tebl/RC-Light-System/documentation/datasheet/rgb_led.png

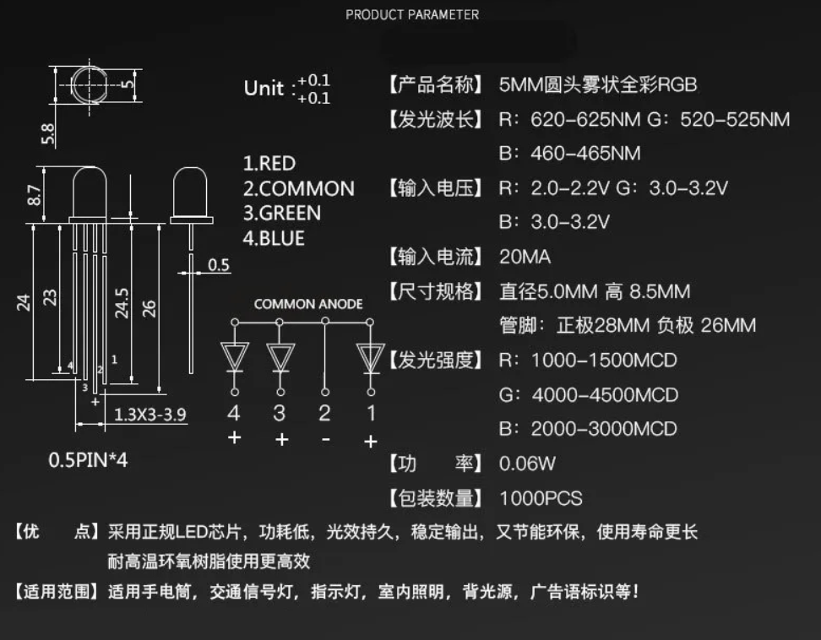
documentation/datasheet/rgb_led.png
