tebl/RC-Light-System/gallery/RC Dashboard Digispark.png

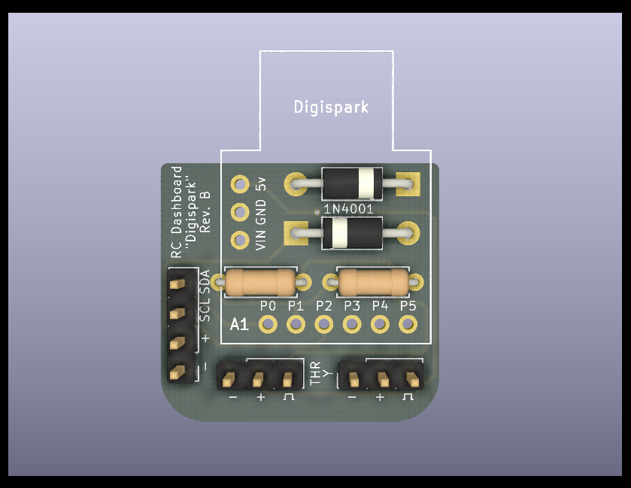
gallery/RC Dashboard Digispark.png
