tebl/RC-Light-System/gallery/RC Dashboard SuperMini2.png

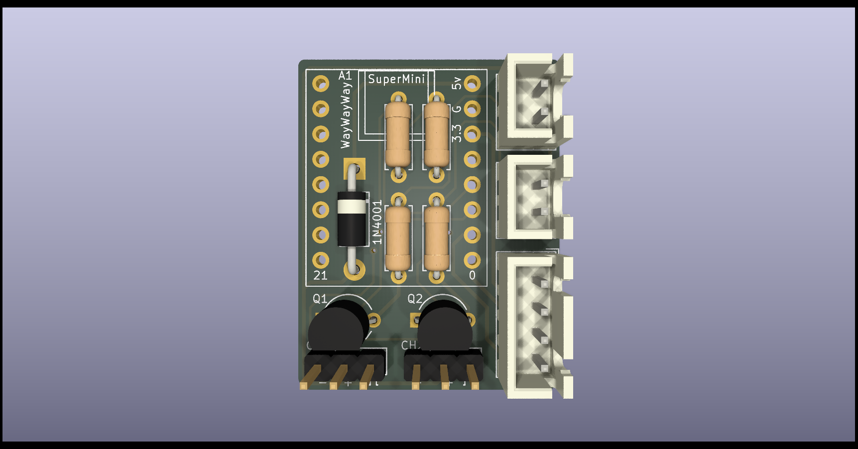
gallery/RC Dashboard SuperMini2.png
