tebl/RC-Light-System/gallery/RC Dashboard SuperMini.png

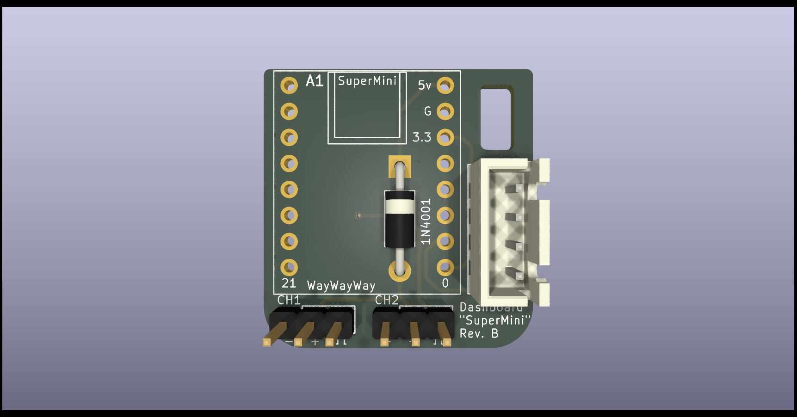
gallery/RC Dashboard SuperMini.png
