tebl/RC-Light-System/gallery/RC Exhaust System RGB.png

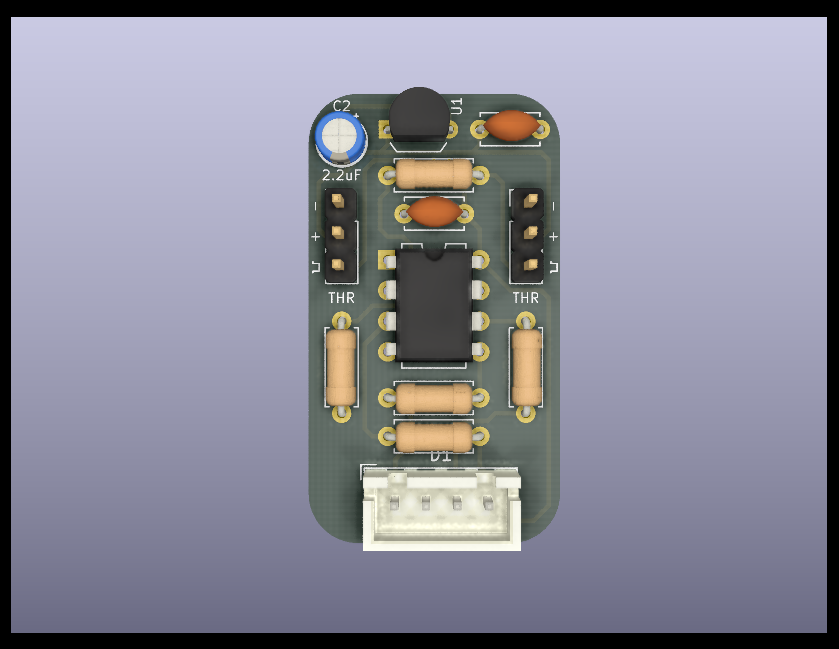
gallery/RC Exhaust System RGB.png
