tebl/RC-Light-System/gallery/RC Light System Output Mini.png

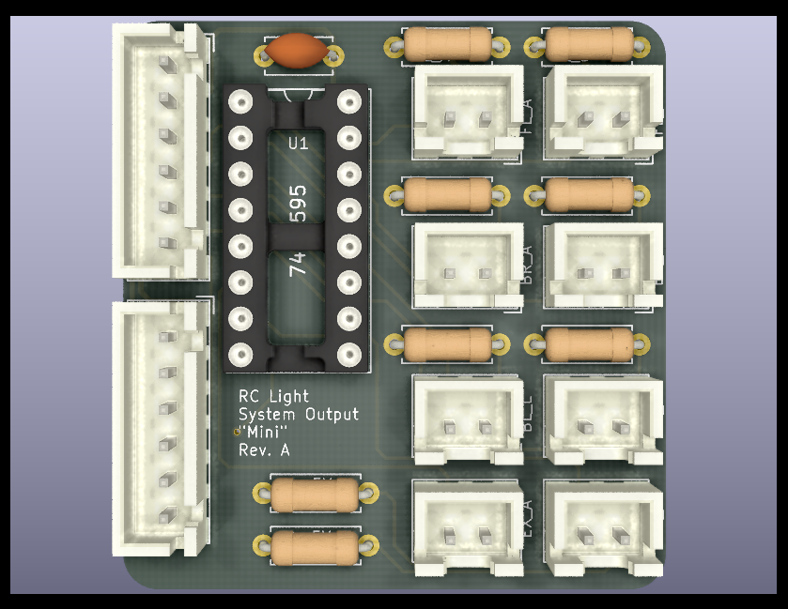
gallery/RC Light System Output Mini.png
