tebl/RC-Light-System/gallery/RC Light System.png

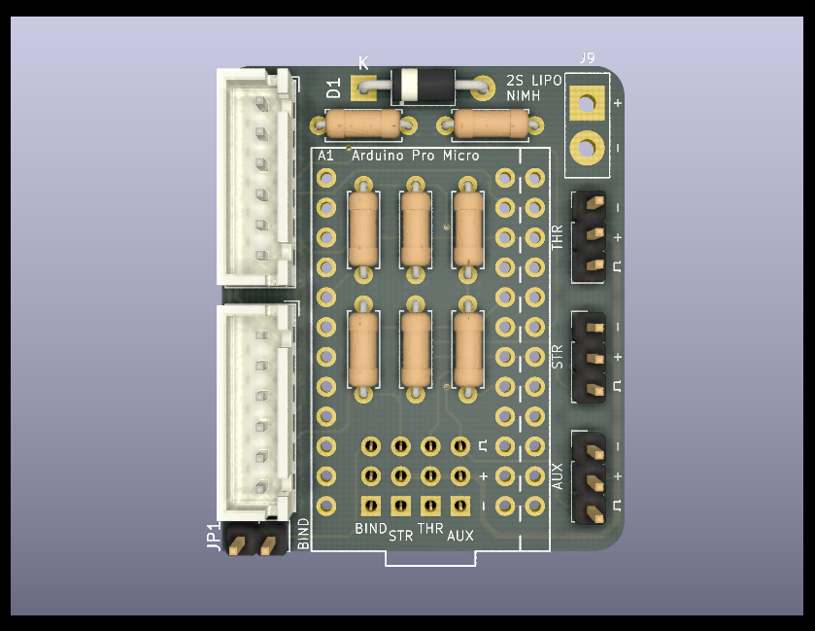
gallery/RC Light System.png
