tebl/RC-Light-System/gallery/RC SCX10.3 Rock Light.png

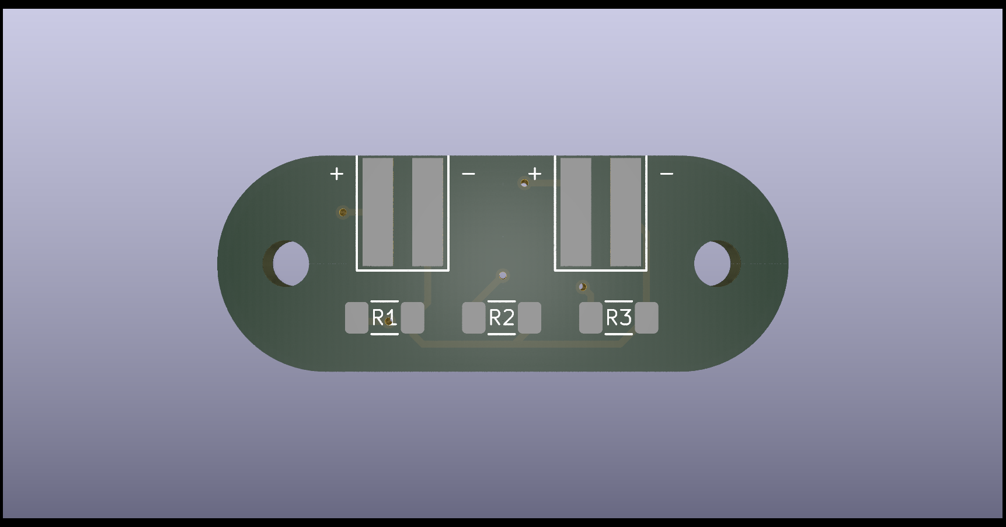
gallery/RC SCX10.3 Rock Light.png
