tebl/RC-Light-System/gallery/build_dashboard_002.jpg

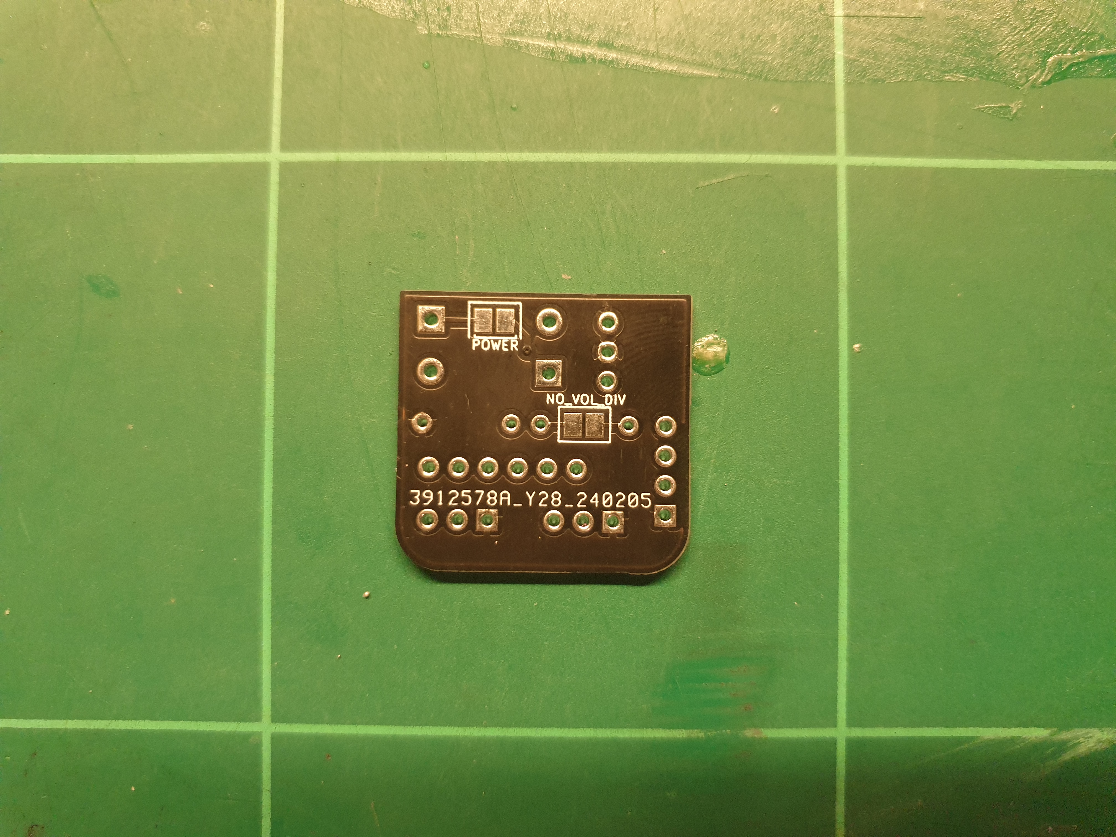
gallery/build_dashboard_002.jpg
