tebl/RC-Light-System/gallery/build_dashboard_012.jpg

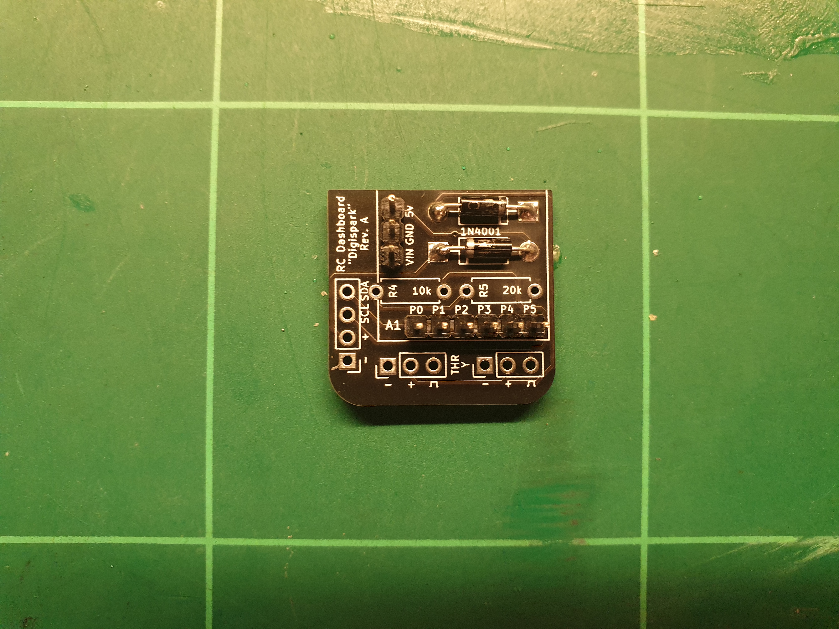
gallery/build_dashboard_012.jpg
