tebl/RC-Light-System/gallery/build_dashboard_013.jpg

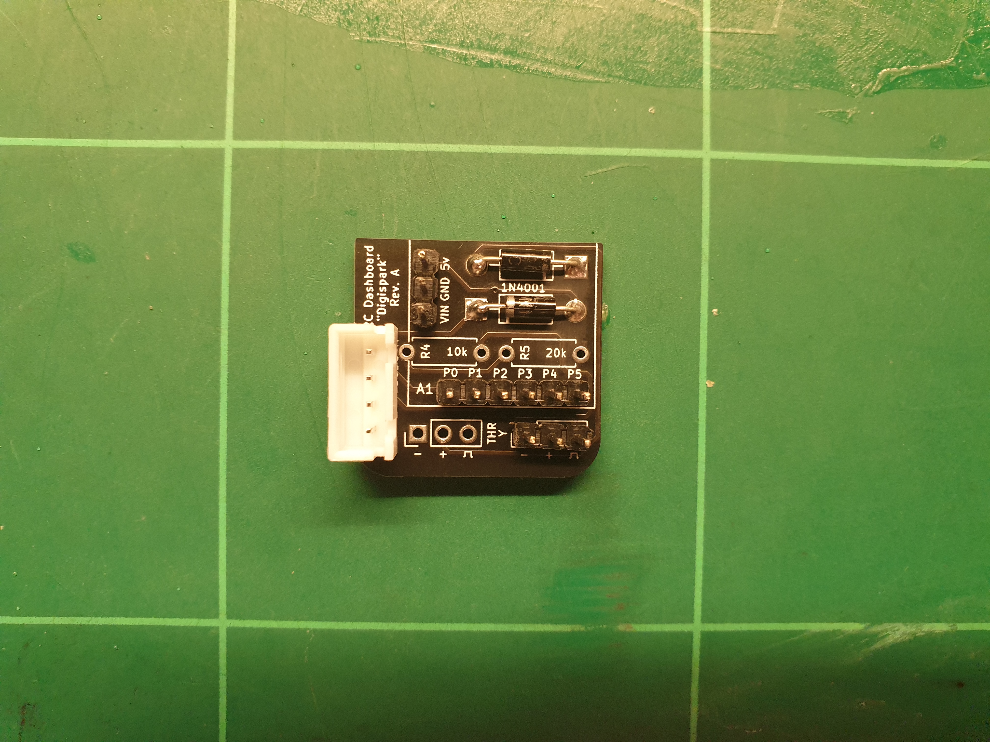
gallery/build_dashboard_013.jpg
