tebl/RC-Light-System/gallery/build_dashboard_014.jpg

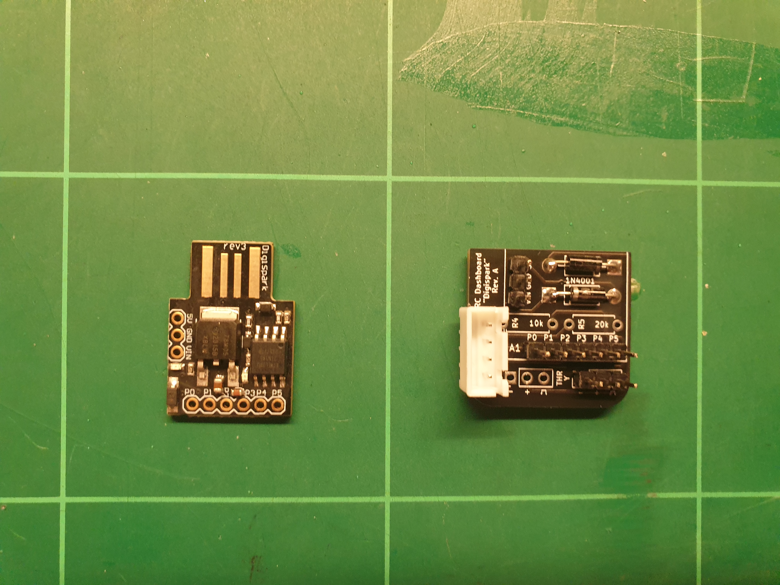
gallery/build_dashboard_014.jpg
