tebl/RC-Light-System/gallery/build_dashboard_015.jpg

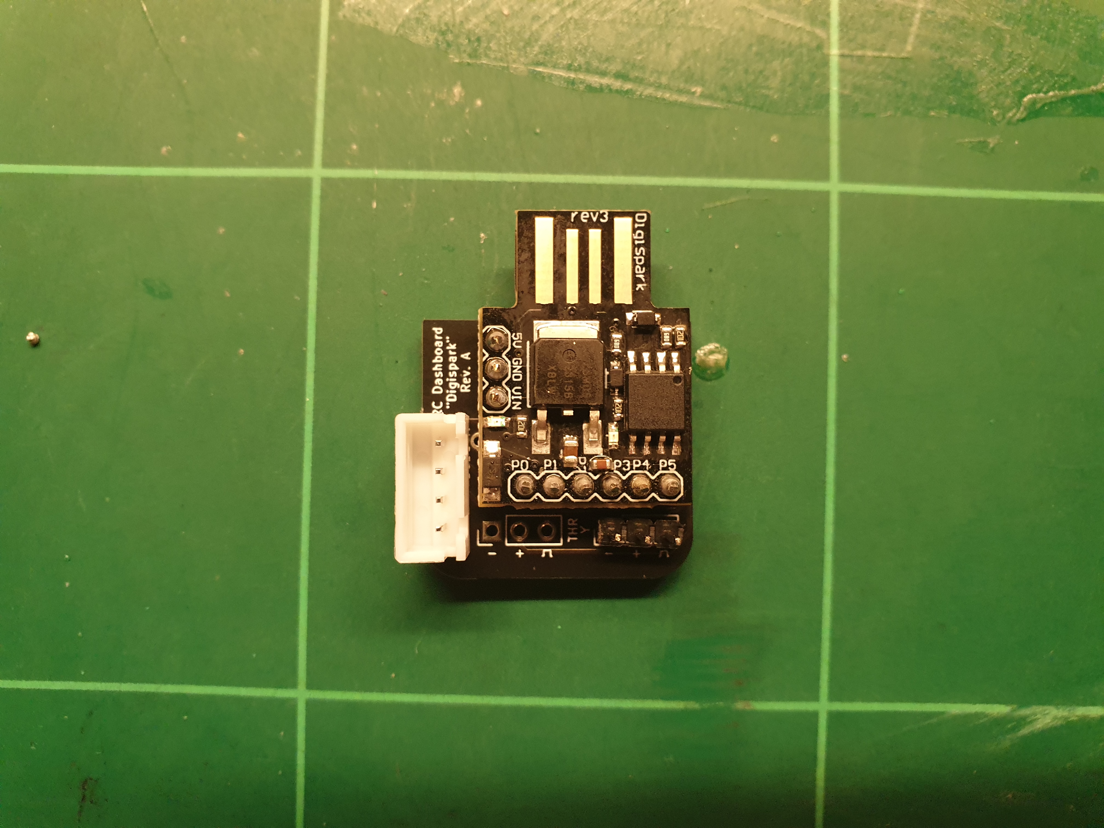
gallery/build_dashboard_015.jpg
