tebl/RC-Light-System/gallery/build_dashboard_020.jpg

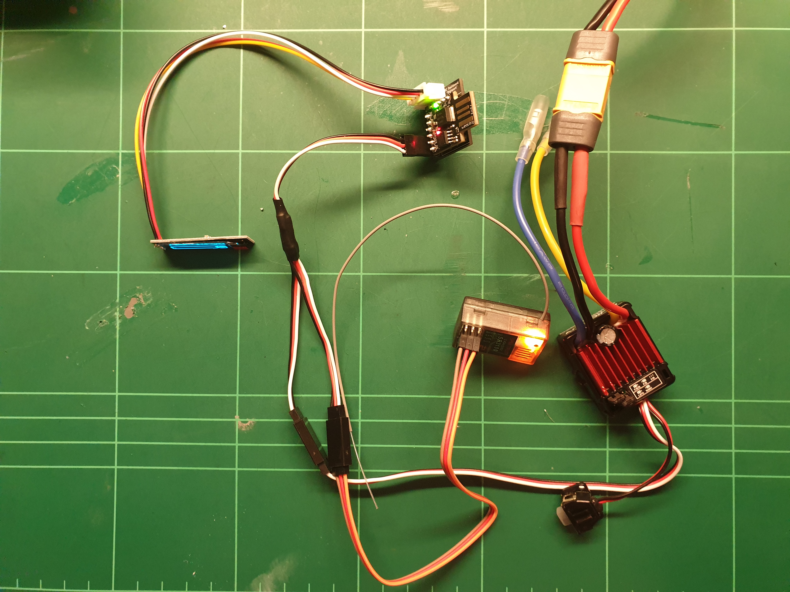
gallery/build_dashboard_020.jpg
