tebl/RC-Light-System/gallery/build_dashboard_021.jpg

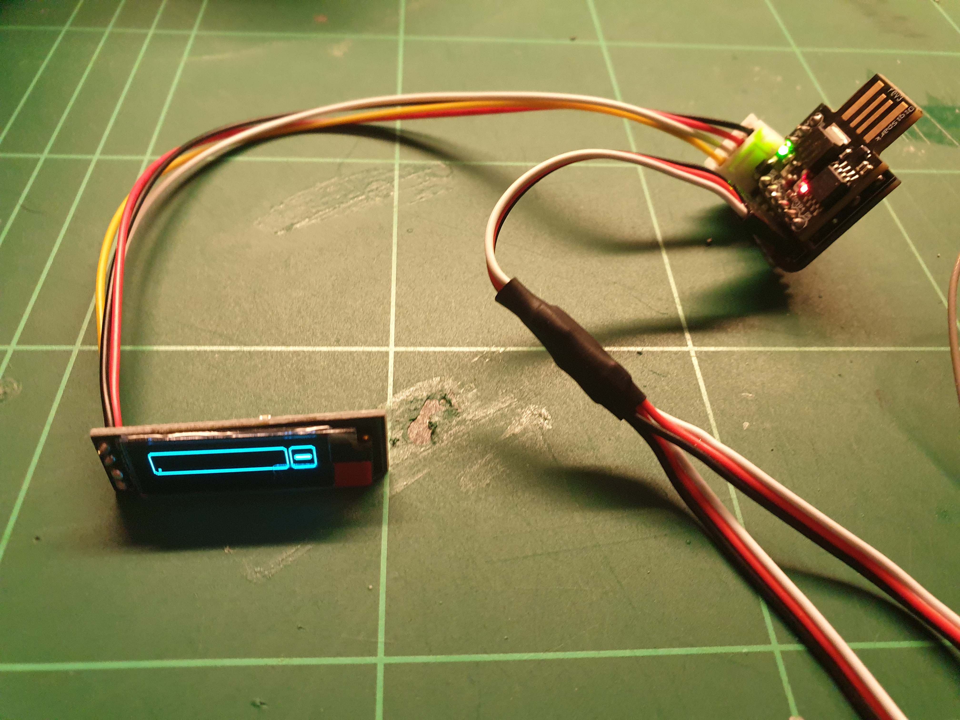
gallery/build_dashboard_021.jpg
